shuvipas/graduation_project/revised current source.kicad_sch

## KiCad design revised current source.kicad_sch (2023-03-28, last stored version)

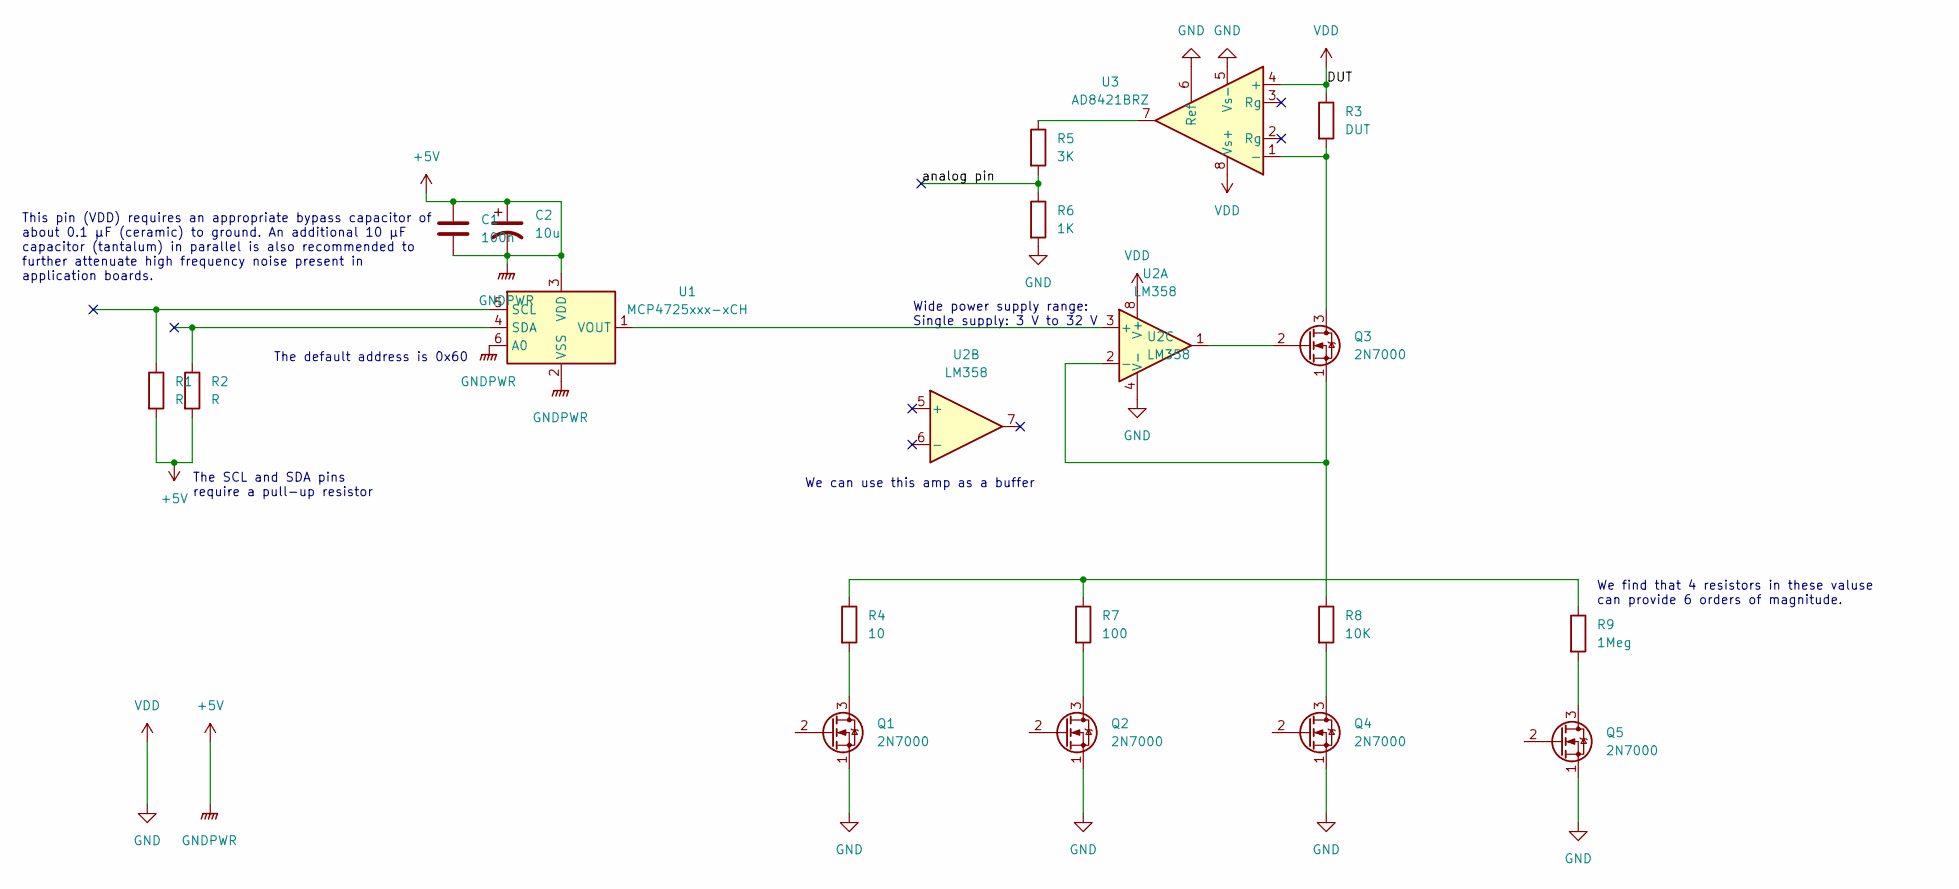
[picture p11: schematic revised current source.kicad_sch]

Parts:
C1: 100n
C2: 10u
Q1, Q2, Q3, Q4, Q5: 2N7000; TO-92_Inline
R1, R2: R
R3: DUT
R4: 10
R5: 3K
R6: 1K
R7: 100
R8: 10K
R9: 1Meg
U1: MCP4725xxx-xCH; SOT-23-6
U2: LM358; DIP-8_W7.62mm_Socket
U3: AD8421BRZ; SOIC-8W_5.3x5.3mm_P1.27mm

Connections:
+5V: C1.1, C1.2, C2.1, C2.2, R1.2, R2.2, U1.2 (VSS), U1.3 (VDD), U1.6 (A0)
GND: Q1.1 (S), Q2.1 (S), Q4.1 (S), Q5.1 (S), R3.1, R6.2, U2.4 (V-), U2.8 (V+), U3.4 (+), U3.5 (Vs-), U3.6 (Ref), U3.8 (Vs+)
unnamed: Q1.3 (D), R4.2
unnamed: Q2.3 (D), R7.2
unnamed: Q3.1 (S), R8.1, U2.2 (-)
unnamed: Q3.2 (G), U2.1
unnamed: Q3.3 (D), R3.2, U3.1 (-)
unnamed: Q4.3 (D), R8.2
unnamed: Q5.3 (D), R9.2
unnamed: R1.1, U1.5 (SCL)
unnamed: R2.1, U1.4 (SDA)
unnamed: R4.1, R7.1, R9.1
unnamed: R5.1, U3.7
unnamed: U1.1 (VOUT), U2.3 (+)
analog pin: R5.2, R6.1

Notes on the sheet:
This pin (VDD) requires an appropriate bypass capacitor of about 0.1 µF (ceramic) to ground. An additional 10 µF capacitor (tantalum) in parallel is also recommended to further attenuate high frequency noise present in application boards.
We can use this amp as a buffer
The default address is 0x60
We find that 4 resistors in these valuse can provide 6 orders of magnitude.
The SCL and SDA pins require a pull-up resistor
Wide power supply range: Single supply: 3 V to 32 V
